Almo-ond-tech/ringotchi/docs/sprite_expressions/sprite_sad2.png

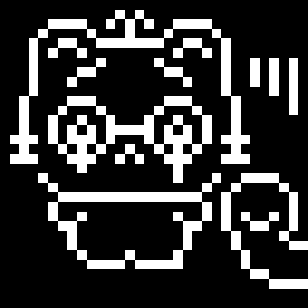
docs/sprite_expressions/sprite_sad2.png
